johnmgreenwell/gba-bridge/cad/gba_bridge_v2.sch

## KiCad design cad/gba_bridge_v2.sch (2021-10-09)

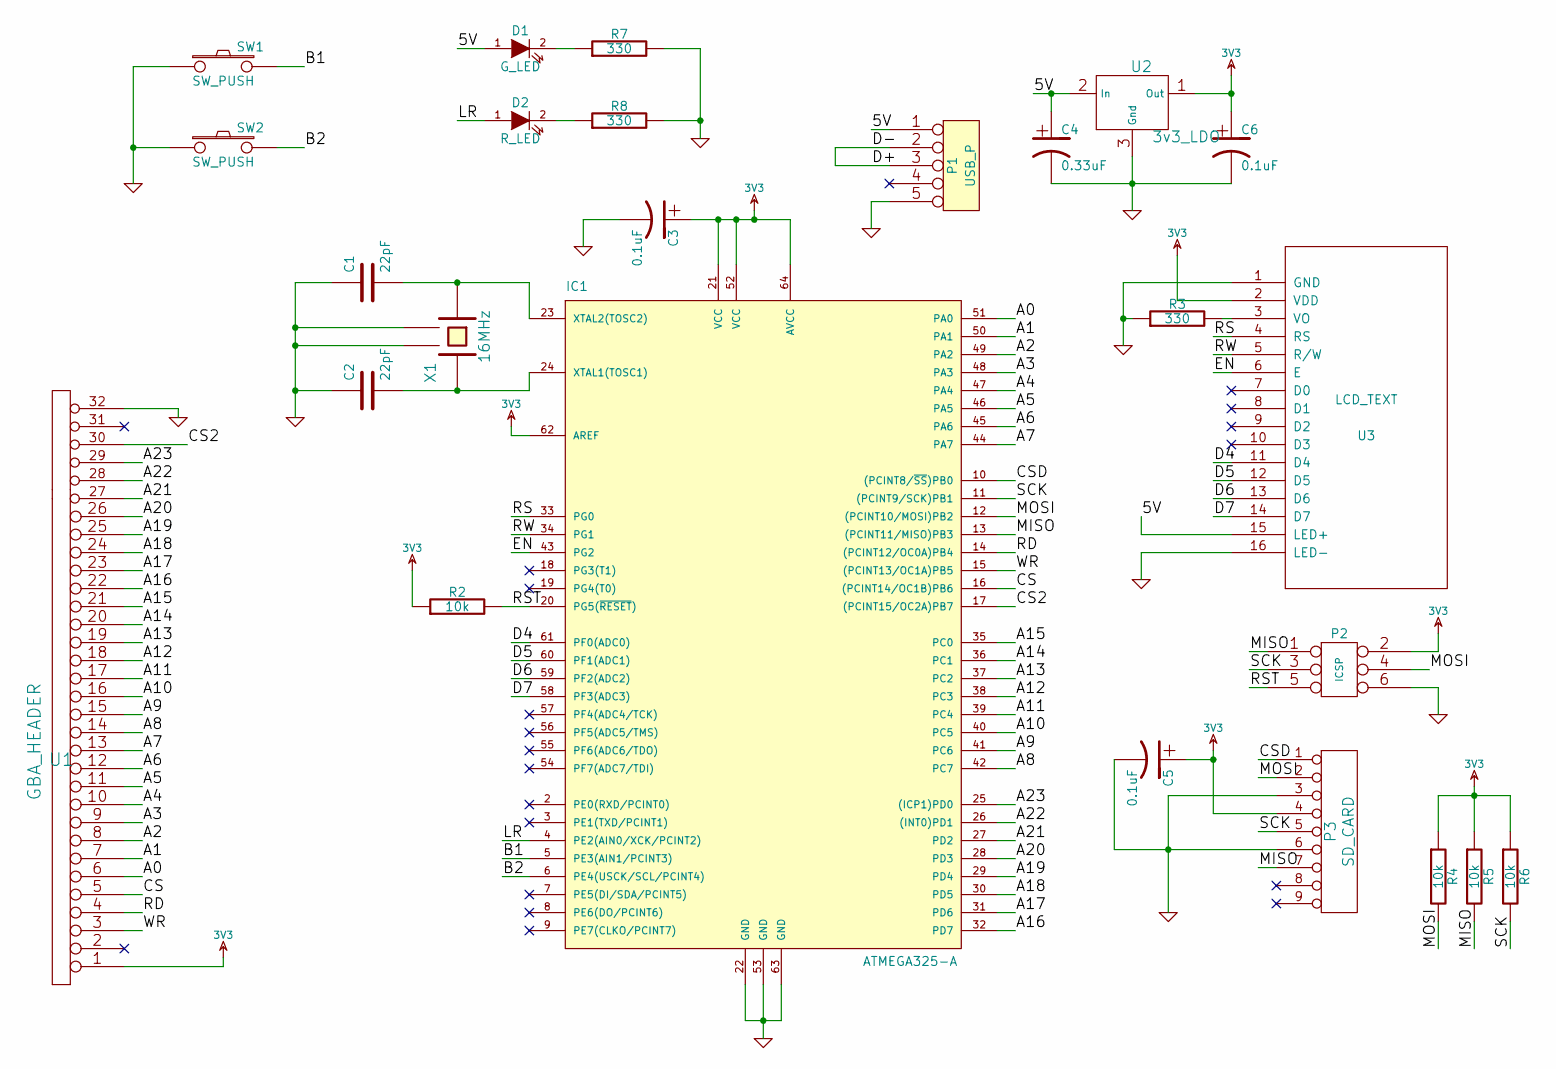
[picture p8: schematic gba_bridge_v2.sch]

Parts:
C1, C2: 22pF
C3, C5, C6: 0.1uF
C4: 0.33uF
D1: G_LED
D2: R_LED
IC1: ATMEGA325-A; TQFP64
P1: USB_P
P2: ICSP
P3: SD_CARD
R2, R4, R5, R6: 10k
R3, R7, R8: 330
SW1, SW2: SW_PUSH
U1: GBA_HEADER
U2: 3v3_LDO
U3: LCD_TEXT; MODULE
X1: 16MHz

Connections:
3V3: C3.1, C5.1, C6.1, IC1.21 (VCC), IC1.52 (VCC), IC1.62 (AREF), IC1.64 (AVCC), P2.2, P3.4, R2.1, R4.1, R5.1, R6.1, U1.1 (VCC), U2.1 (Out), U3.2 (VDD)
5V: C4.1, D1.1 (A), P1.1, U2.2 (In), U3.15 (LED+)
A0: IC1.51 (PA0), U1.6 (A0)
A1: IC1.50 (PA1), U1.7 (A1)
A2: IC1.49 (PA2), U1.8 (A2)
A3: IC1.48 (PA3), U1.9 (A3)
A4: IC1.47 (PA4), U1.10 (A4)
A5: IC1.46 (PA5), U1.11 (A5)
A6: IC1.45 (PA6), U1.12 (A6)
A7: IC1.44 (PA7), U1.13 (A7)
A8: IC1.42 (PC7), U1.14 (A8)
A9: IC1.41 (PC6), U1.15 (A9)
A10: IC1.40 (PC5), U1.16 (A10)
A11: IC1.39 (PC4), U1.17 (A11)
A12: IC1.38 (PC3), U1.18 (A12)
A13: IC1.37 (PC2), U1.19 (A13)
A14: IC1.36 (PC1), U1.20 (A14)
A15: IC1.35 (PC0), U1.21 (A15)
A16: IC1.32 (PD7), U1.22 (D0)
A17: IC1.31 (PD6), U1.23 (D1)
A18: IC1.30 (PD5), U1.24 (D2)
A19: IC1.29 (PD4), U1.25 (D3)
A20: IC1.28 (PD3), U1.26 (D4)
A21: IC1.27 (PD2), U1.27 (D5)
A22: IC1.26 ((INT0)PD1), U1.28 (D6)
A23: IC1.25 ((ICP1)PD0), U1.29 (D7)
B1: IC1.5 (PE3(AIN1/PCINT3)), SW1.2
B2: IC1.6 (PE4(USCK/SCL/PCINT4)), SW2.2
CS: IC1.16 ((PCINT14/OC1B)PB6), U1.5 (CS)
CS2: IC1.17 ((PCINT15/OC2A)PB7), U1.30 (CS2)
CSD: IC1.10 ((PCINT8/~SS~)PB0), P3.1
D4: IC1.61 (PF0(ADC0)), U3.11 (D4)
D5: IC1.60 (PF1(ADC1)), U3.12 (D5)
D6: IC1.59 (PF2(ADC2)), U3.13 (D6)
D7: IC1.58 (PF3(ADC3)), U3.14 (D7)
D+: P1.2, P1.3
EN: IC1.43 (PG2), U3.6 (E)
GND: C1.1, C2.1, C3.2, C4.2, C5.2, C6.2, IC1.22 (GND), IC1.53 (GND), IC1.63 (GND), P1.5, P2.6, P3.3, P3.6, R3.1, R7.2, R8.2, SW1.1, SW2.1, U1.32 (GND), U2.3 (Gnd), U3.1 (GND), U3.16 (LED-), X1.2 (GND), X1.4 (GND)
LR: D2.1 (A), IC1.4 (PE2(AIN0/XCK/PCINT2))
MISO: IC1.13 ((PCINT11/MISO)PB3), P2.1, P3.7, R5.2
MOSI: IC1.12 ((PCINT10/MOSI)PB2), P2.4, P3.2, R4.2
unnamed: C1.2, IC1.23 (XTAL2(TOSC2)), X1.1
unnamed: C2.2, IC1.24 (XTAL1(TOSC1)), X1.3
unnamed: D1.2 (K), R7.1
unnamed: D2.2 (K), R8.1
unnamed: R3.2, U3.3 (VO)
RD: IC1.14 ((PCINT12/OC0A)PB4), U1.4 (RD)
RS: IC1.33 (PG0), U3.4 (RS)
RST: IC1.20 (PG5(~RESET~)), P2.5, R2.2
RW: IC1.34 (PG1), U3.5 (R/W)
SCK: IC1.11 ((PCINT9/SCK)PB1), P2.3, P3.5, R6.2
WR: IC1.15 ((PCINT13/OC1A)PB5), U1.3 (WR)
